MakersAsylumIndia/MAP6_Maker_Bee/datasheets/PngItem_3031532.png

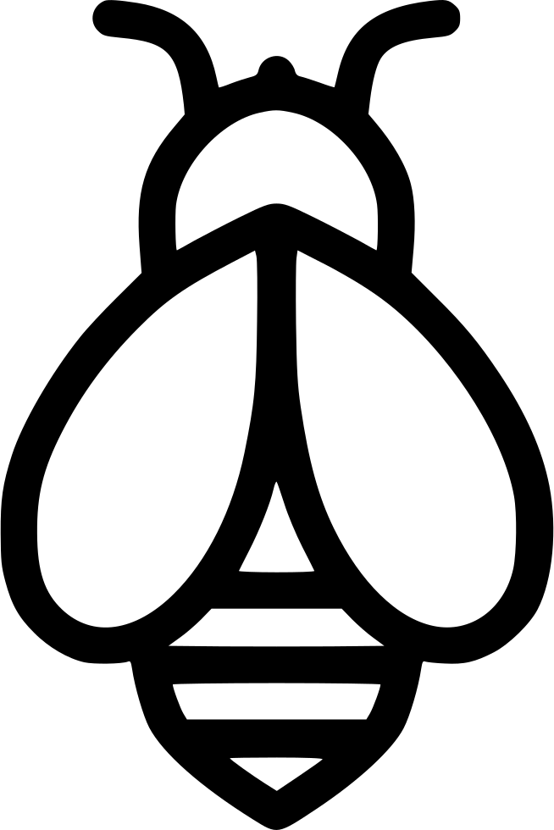
datasheets/PngItem_3031532.png
