MakersAsylumIndia/MAP6_Maker_Bee/kicad/images/MAP6-brd.png

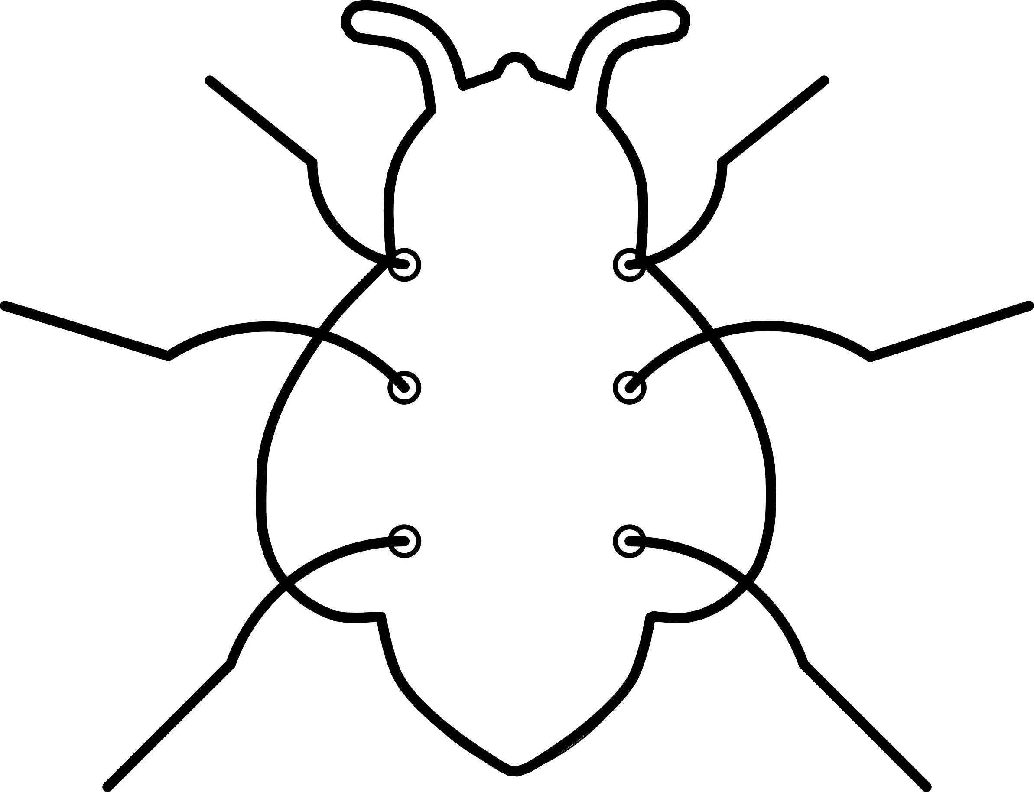
kicad/images/MAP6-brd.png
