MakersAsylumIndia/MAP6_Maker_Bee/kicad/images/MAP6_01.png

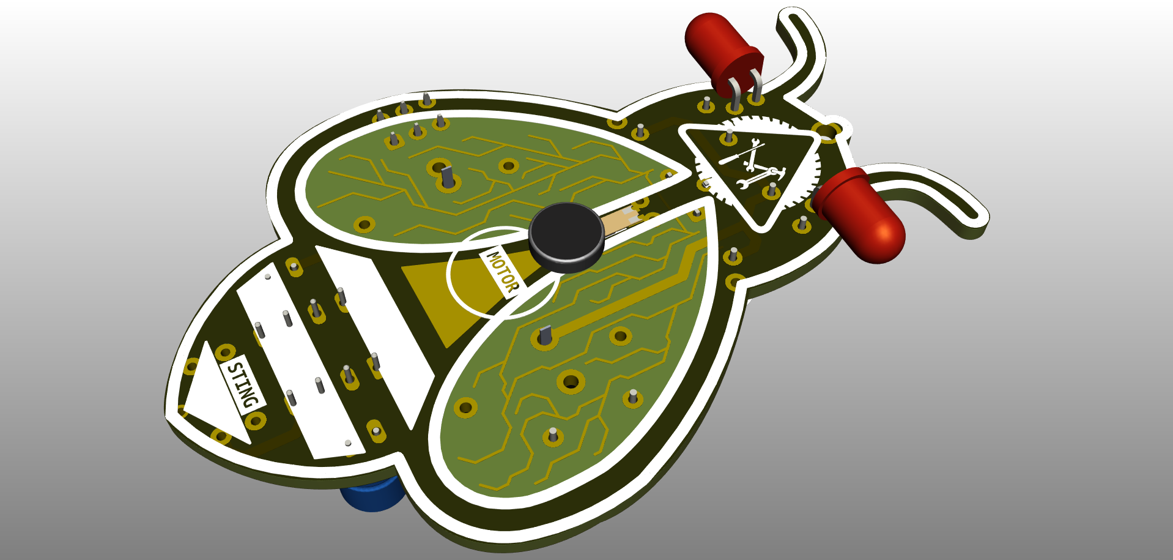
kicad/images/MAP6_01.png
