MakersAsylumIndia/MAP6_Maker_Bee/kicad/images/MAP6_02.png

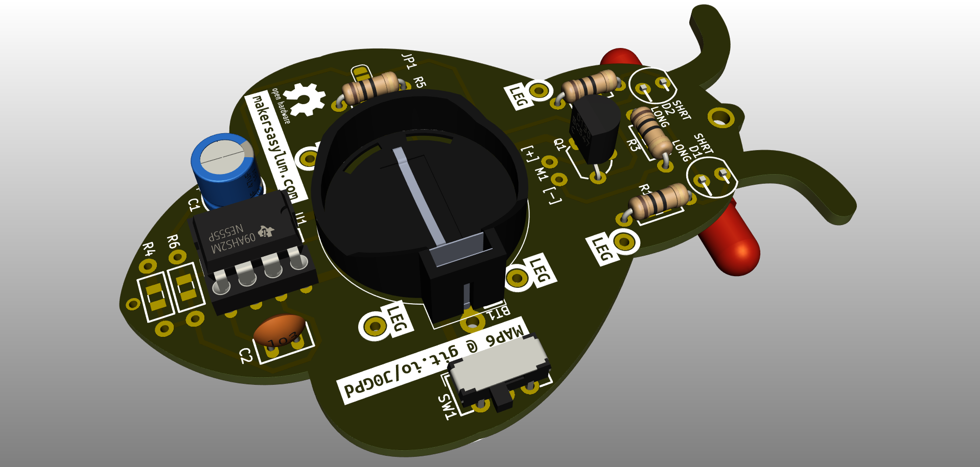
kicad/images/MAP6_02.png
