MakersAsylumIndia/MAP6_Maker_Bee/kicad/images/MAP6_03.png

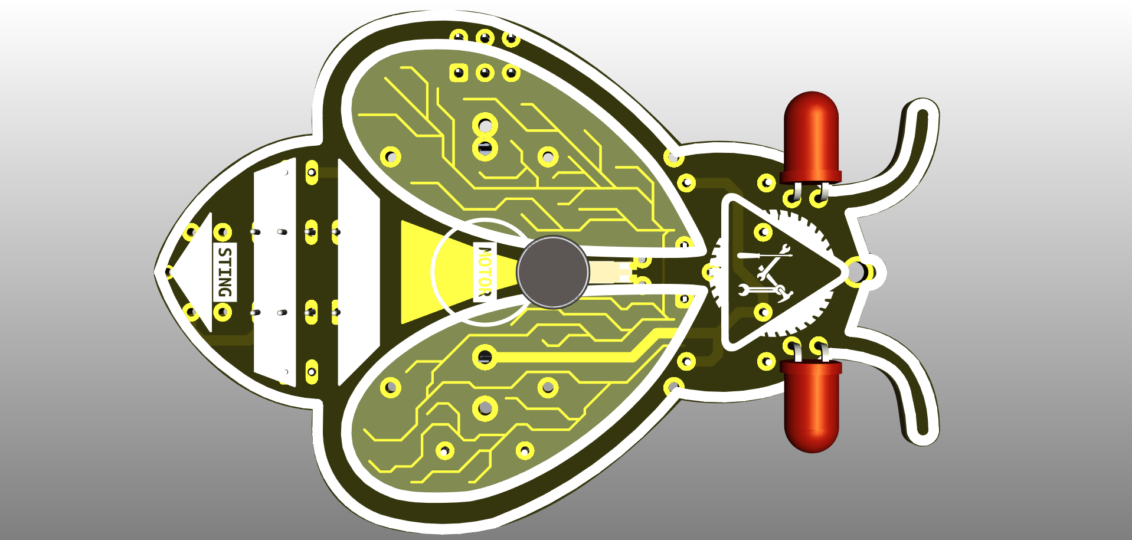
kicad/images/MAP6_03.png
