MakersAsylumIndia/MAP6_Maker_Bee/kicad/images/MAP6_04.png

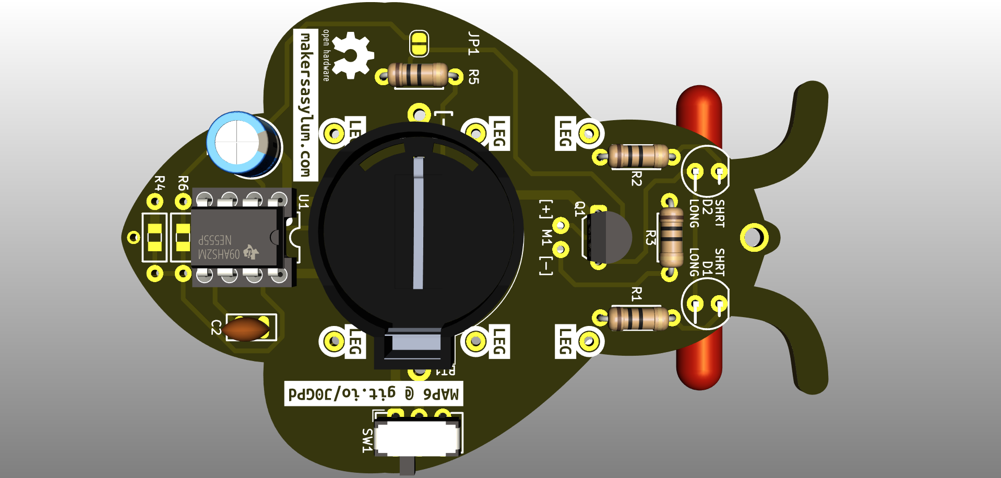
kicad/images/MAP6_04.png
