MakersAsylumIndia/MAP6_Maker_Bee/kicad/images/MAP6_05.png

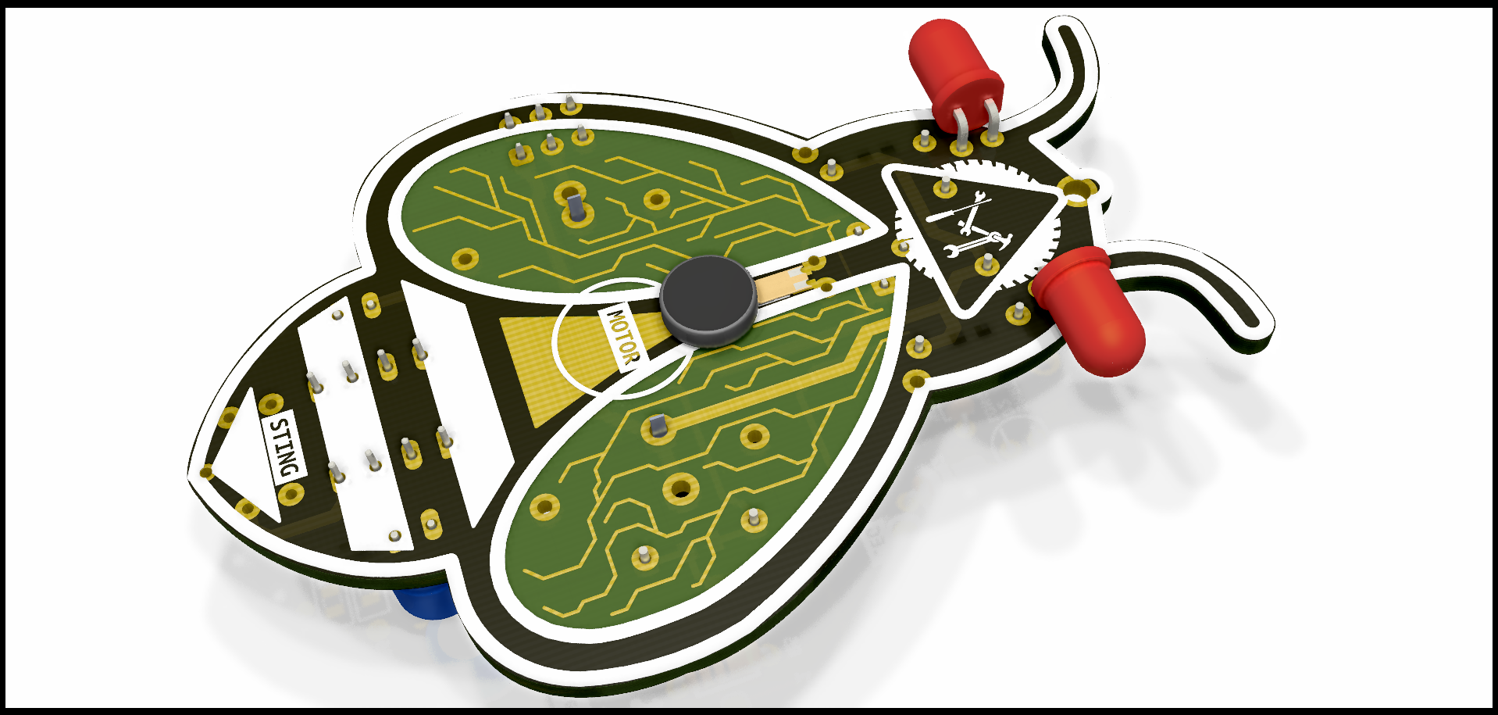
kicad/images/MAP6_05.png
