MakersAsylumIndia/MAP6_Maker_Bee/kicad/images/MAP6_06.png

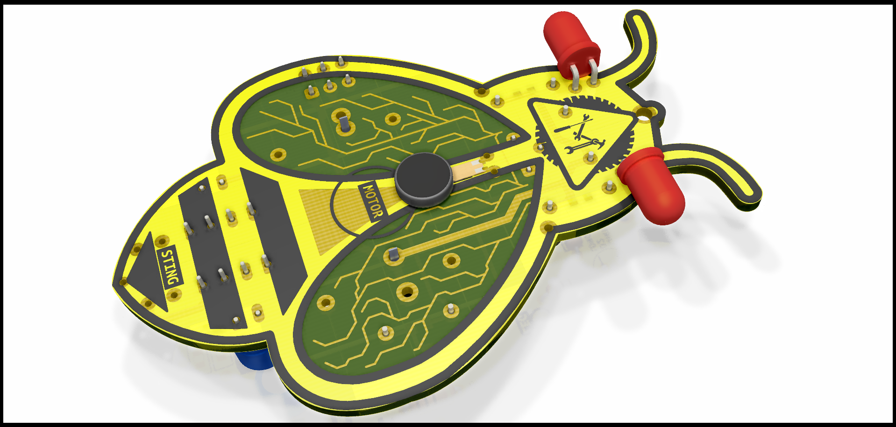
kicad/images/MAP6_06.png
