MakersAsylumIndia/MAP6_Maker_Bee/kicad/images/MAP6_07.png

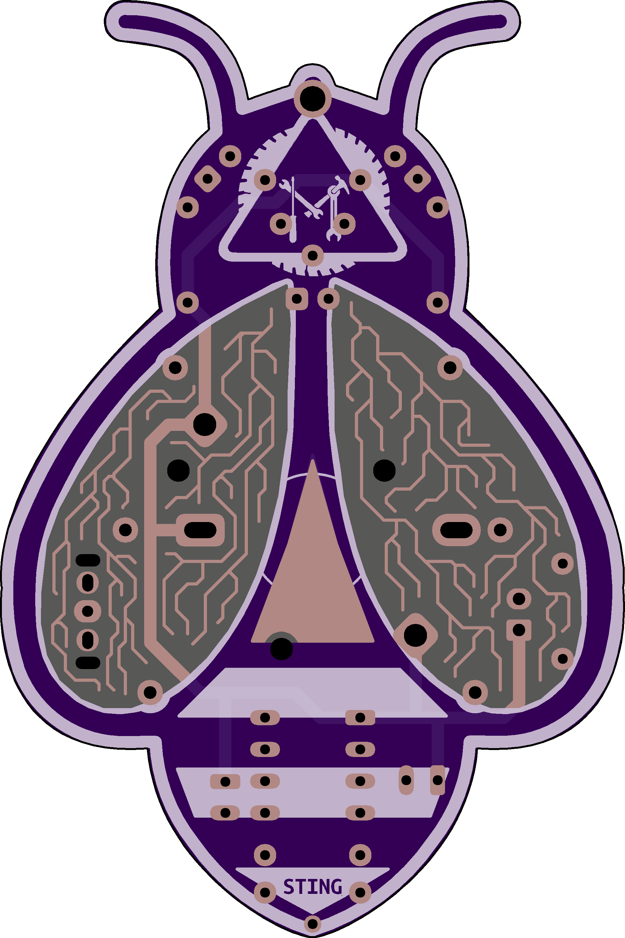
kicad/images/MAP6_07.png
