MakersAsylumIndia/MAP6_Maker_Bee/kicad/images/MAP6_08.png

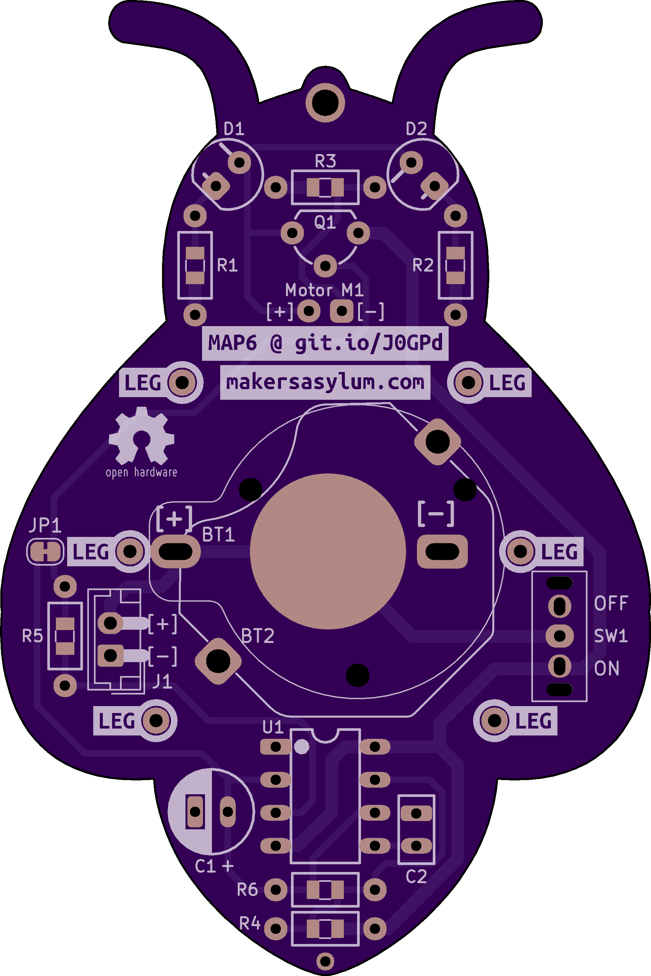
kicad/images/MAP6_08.png
