MakersAsylumIndia/MAP6_Maker_Bee/kicad/images/MAP6_13.png

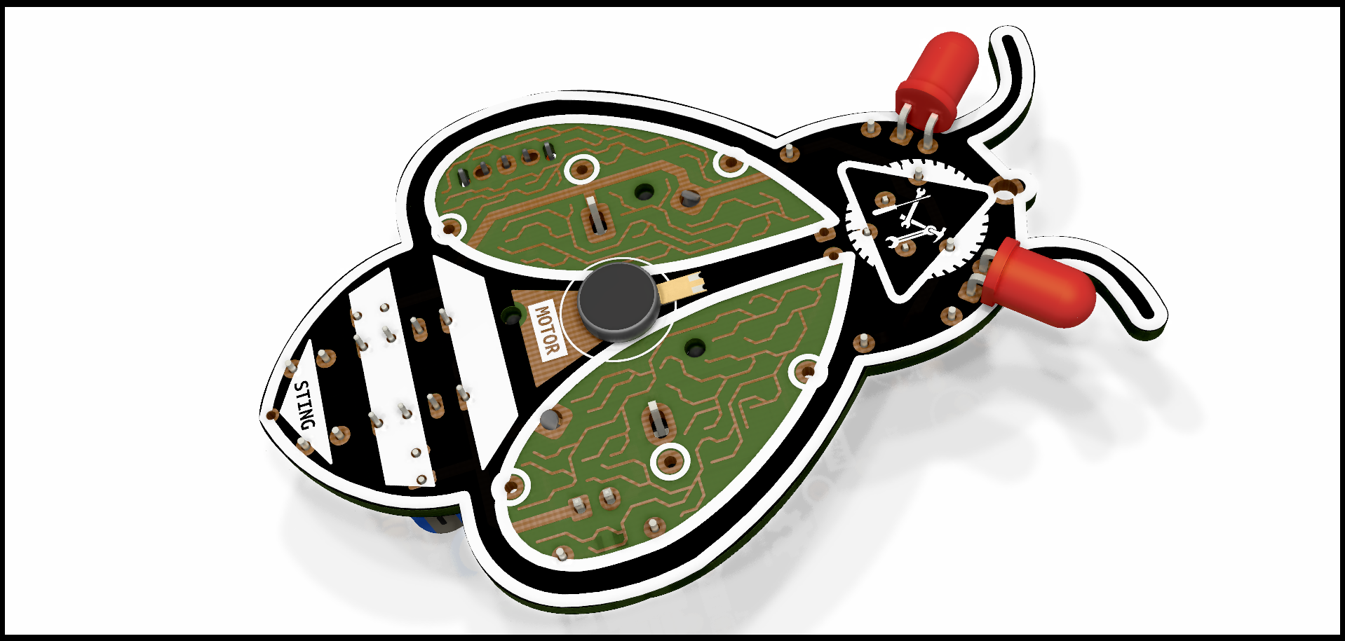
kicad/images/MAP6_13.png
