MakersAsylumIndia/MAP6_Maker_Bee/OSHWA_IN000031.png

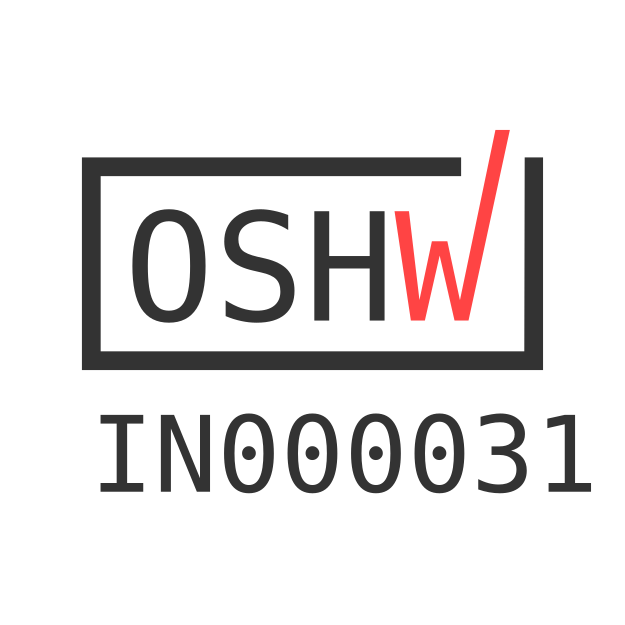
OSHWA_IN000031.png
