MakersAsylumIndia/MAP6_Maker_Bee/renders/map6_06_06_render12.png

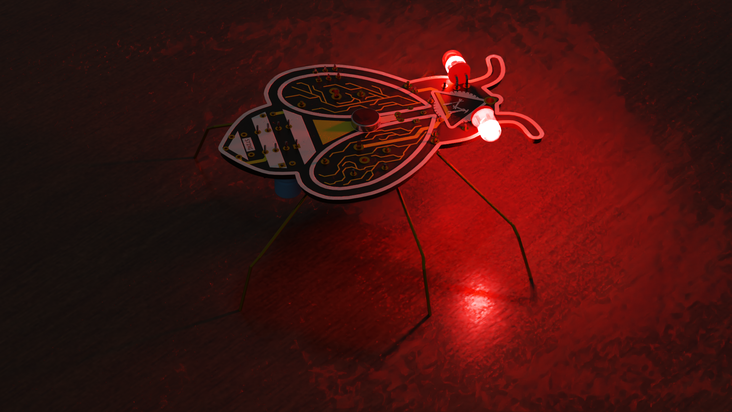
renders/map6_06_06_render12.png
