MakersAsylumIndia/MAP6_Maker_Bee/renders/map6_render02.png

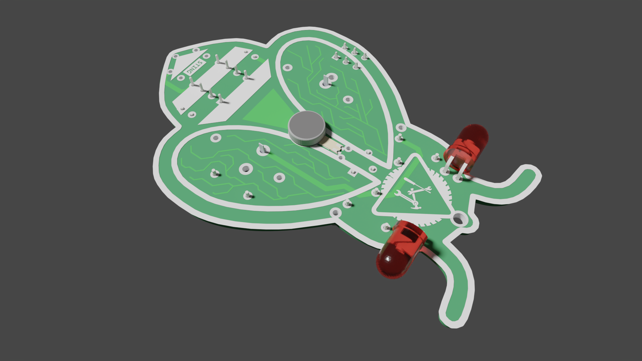
renders/map6_render02.png
