MakersAsylumIndia/MAP6_Maker_Bee/renders/map6_render03.jpg

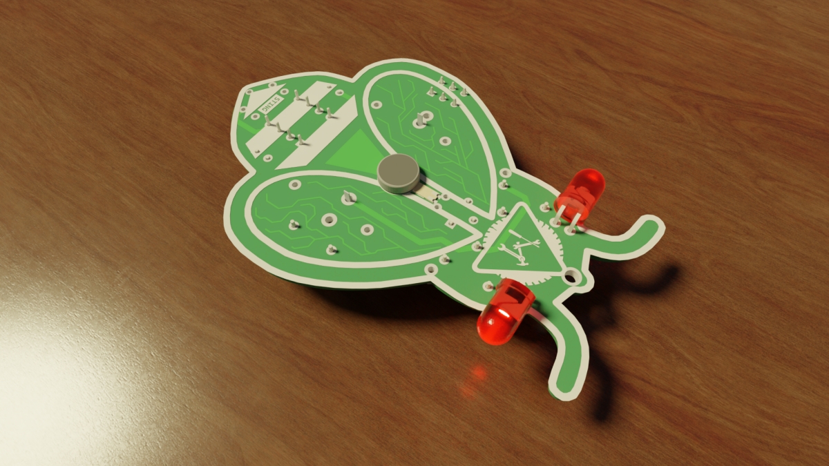
renders/map6_render03.jpg
