MakersAsylumIndia/MAP6_Maker_Bee/renders/map6_render05.jpg

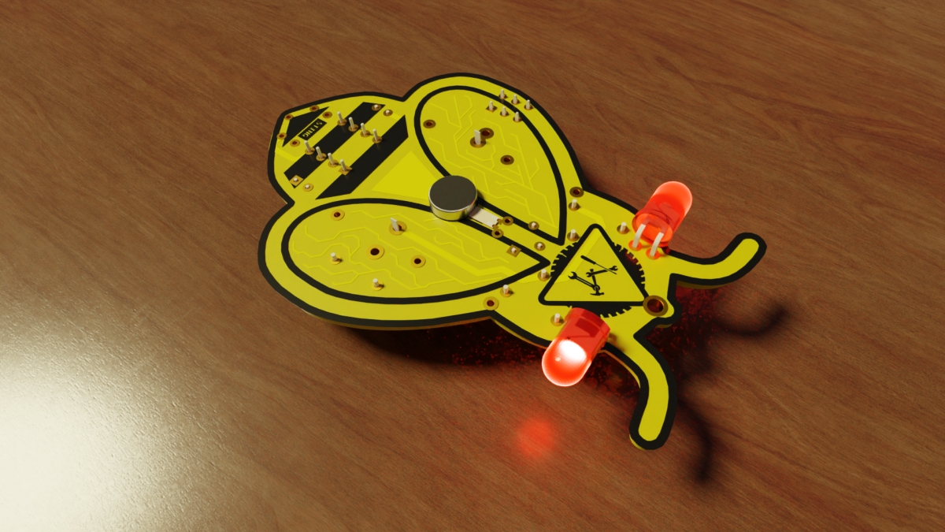
renders/map6_render05.jpg
