MakersAsylumIndia/MAP6_Maker_Bee/renders/map6_render07.jpg

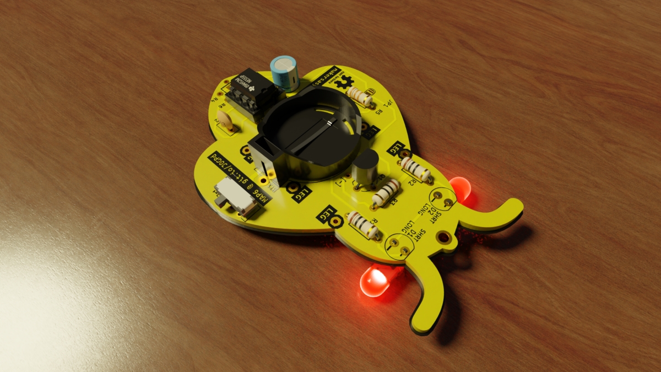
renders/map6_render07.jpg
