MakersAsylumIndia/MAP6_Maker_Bee/renders/map6_render09.jpg

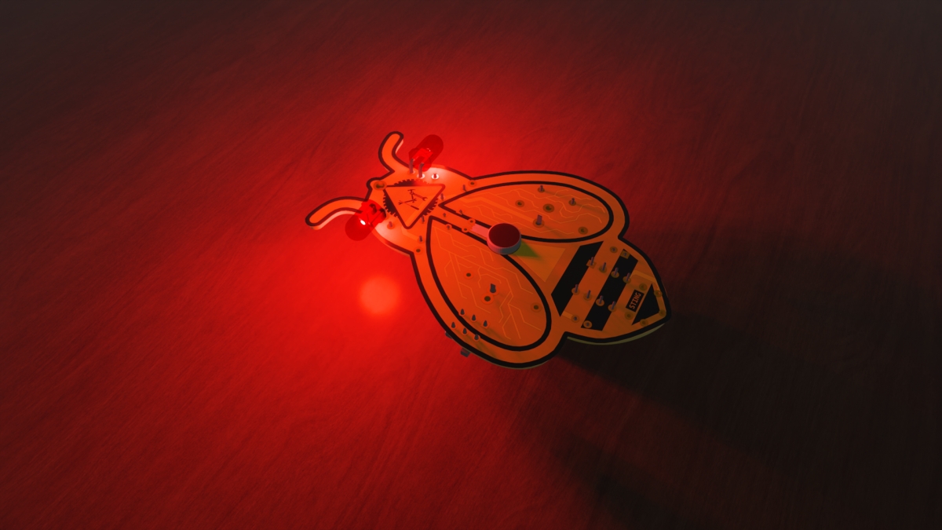
renders/map6_render09.jpg
