MakersAsylumIndia/MAP6_Maker_Bee/renders/map6_render10.jpg

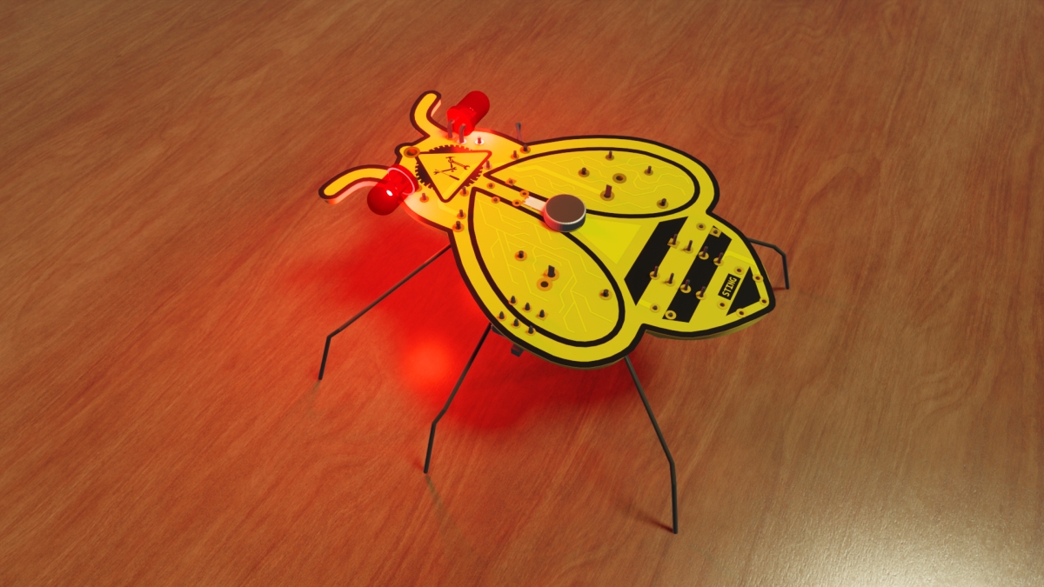
renders/map6_render10.jpg
