MakersAsylumIndia/MAP6_Maker_Bee/renders/map6_render11.png

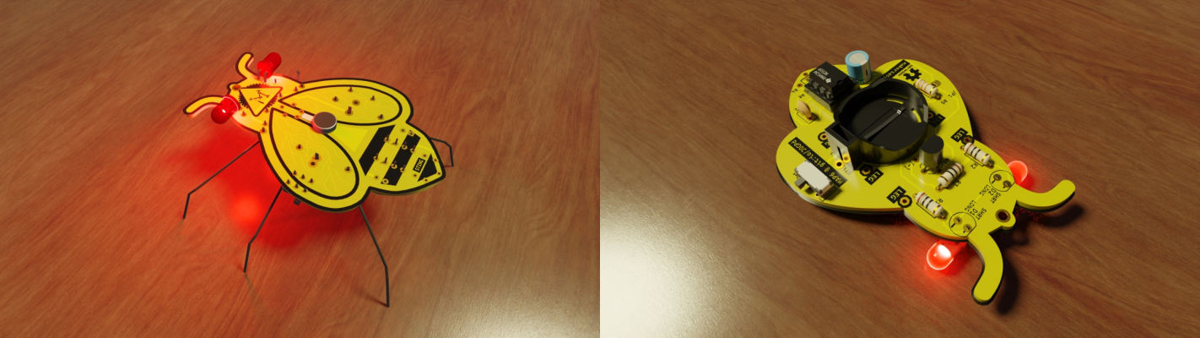
renders/map6_render11.png
