MakersAsylumIndia/MAP6_Maker_Bee/fabricate/PCB_outline/shape_bee5.dxf

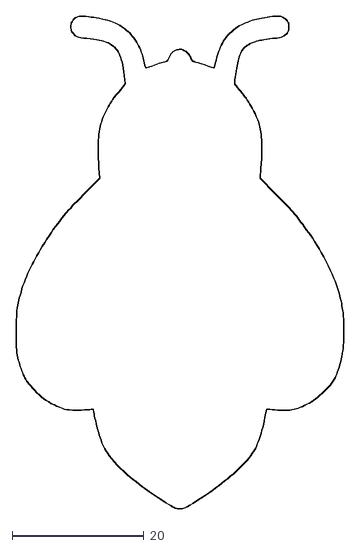
[picture p39: CAD file, 2021-08-18]
fabricate/PCB_outline/shape_bee5.dxf
49.8 x 74.9
