MakersAsylumIndia/MAP6_Maker_Bee/nightly/3d_modules/JST_EH_B3B-EH-A_1x03_P2.50mm_Vertical.step

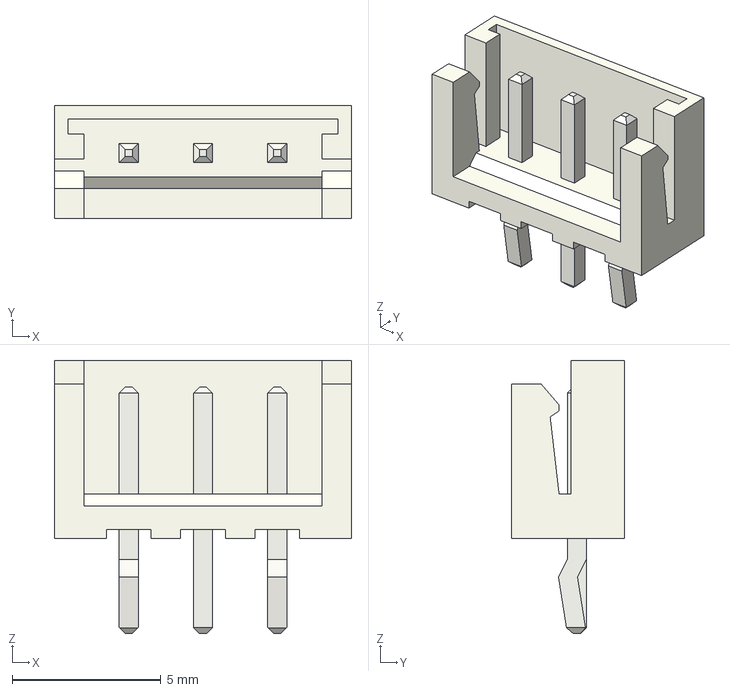
[picture p40: CAD file, 2021-09-08]
nightly/3d_modules/JST_EH_B3B-EH-A_1x03_P2.50mm_Vertical.step
10.0 x 3.80 x 9.20 mm
