MakersAsylumIndia/MAP6_Maker_Bee/fabricate/PCB_outline/outline_bee.dxf

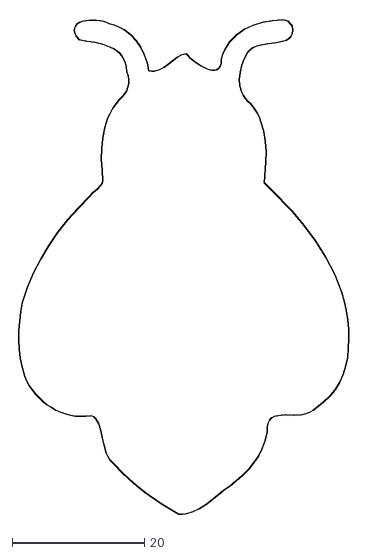
[picture p41: CAD file, 2021-08-18]
fabricate/PCB_outline/outline_bee.dxf
51.0 x 75.5
