MakersAsylumIndia/MAP6_Maker_Bee/kicad/3d_modules/JST_EH_B2B-EH-A_1x02_P2.50mm_Vertical.step

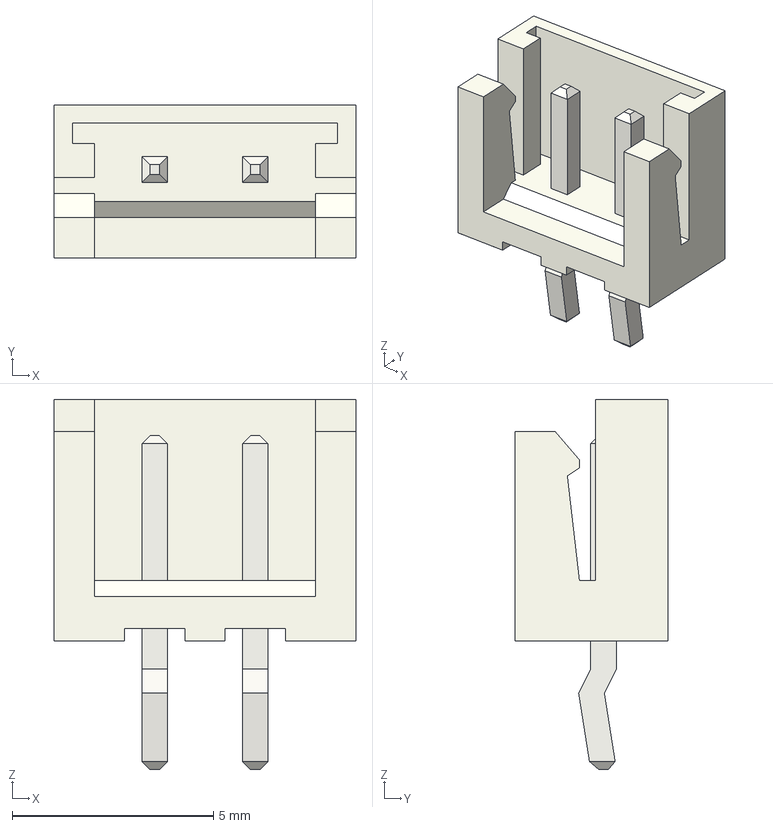
[picture p42: CAD file, 2021-09-08]
kicad/3d_modules/JST_EH_B2B-EH-A_1x02_P2.50mm_Vertical.step
7.50 x 3.80 x 9.20 mm
