MakersAsylumIndia/MAP6_Maker_Bee/nightly/3d_modules/CR2032_cyl_cp.step

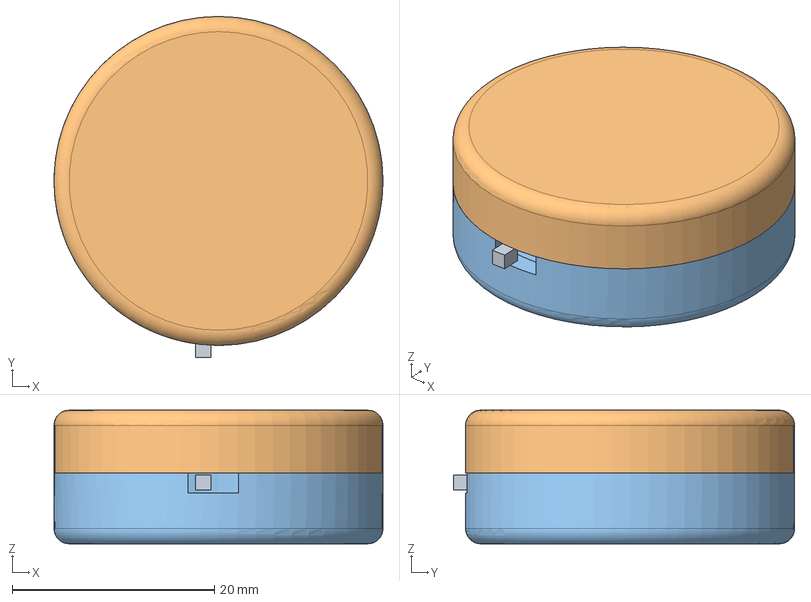
[picture p44: CAD file, 2021-09-07]
nightly/3d_modules/CR2032_cyl_cp.step
32.5 x 33.7 x 13.2 mm
