MakersAsylumIndia/MAP6_Maker_Bee/fabricate/PCB_outline/shape_bee3.dxf

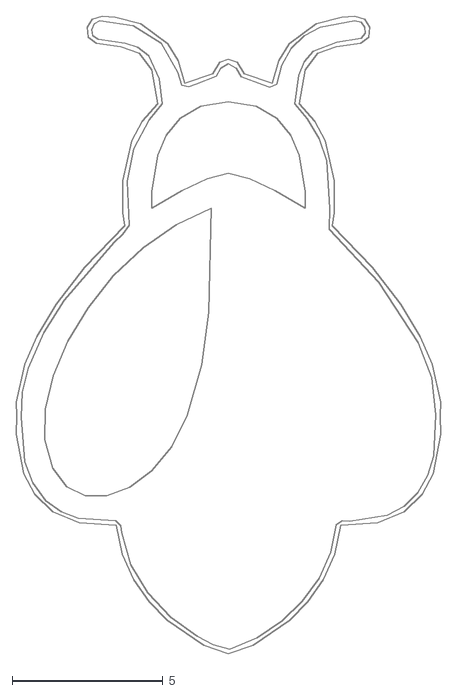
[picture p45: CAD file, 2021-08-18]
fabricate/PCB_outline/shape_bee3.dxf
14.1 x 21.1
