MakersAsylumIndia/MAP6_Maker_Bee/fabricate/PCB_outline/outline_bee2.dxf

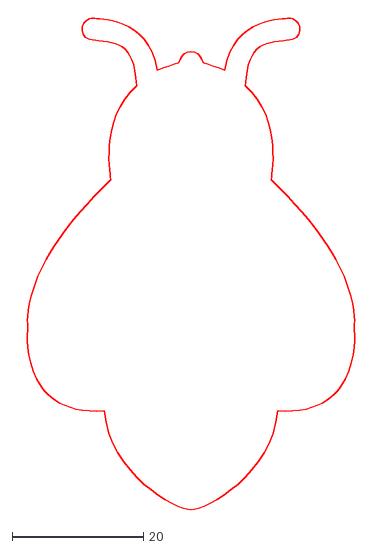
[picture p46: CAD file, 2021-08-18]
fabricate/PCB_outline/outline_bee2.dxf
53.2 x 75.2
