MakersAsylumIndia/MAP6_Maker_Bee/fabricate/PCB_outline/shape_bee4.dxf

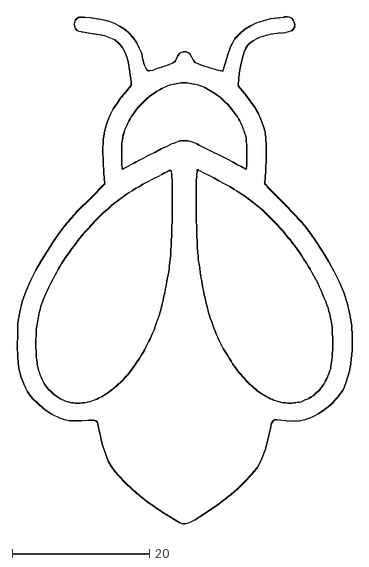
[picture p47: CAD file, 2021-08-18]
fabricate/PCB_outline/shape_bee4.dxf
49.0 x 74.3
