MakersAsylumIndia/MAP6_Maker_Bee/nightly/3d_modules/Led5mm_right_FC.step

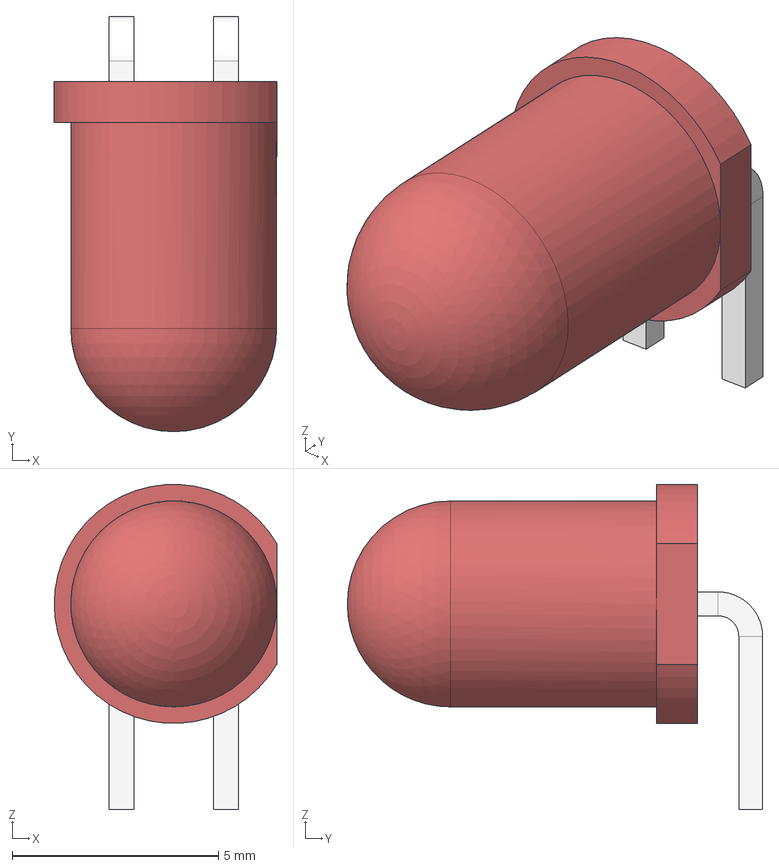
[picture p48: CAD file, 2021-08-23]
nightly/3d_modules/Led5mm_right_FC.step
5.40 x 10.1 x 7.89 mm
