MakersAsylumIndia/MAP6_Maker_Bee/nightly/3d_modules/TO-92_BC547_FC.step

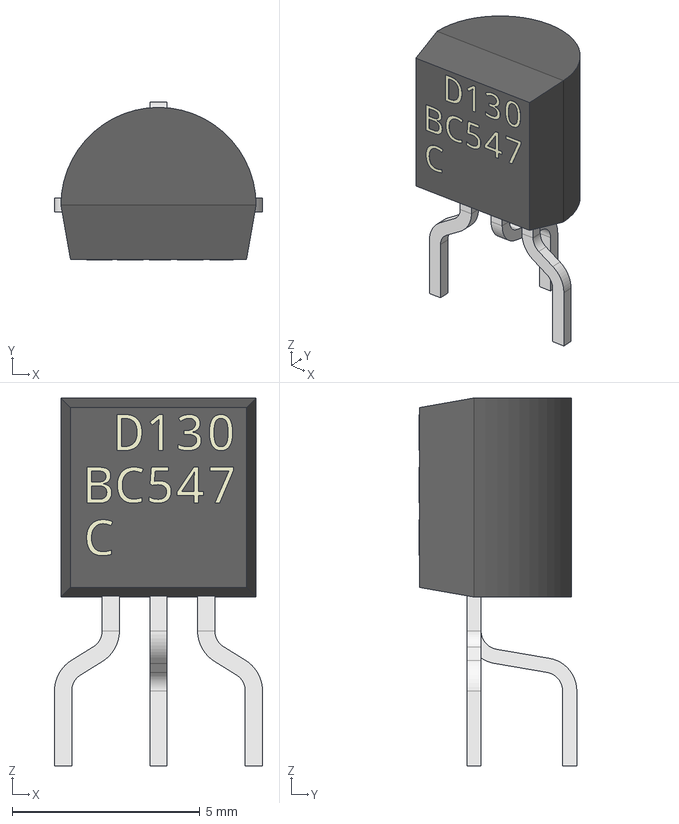
[picture p49: CAD file, 2021-08-23]
nightly/3d_modules/TO-92_BC547_FC.step
5.54 x 4.20 x 9.80 mm
