MakersAsylumIndia/MAP6_Maker_Bee/nightly/3d_modules/C_Disc_D50mm_W25mm_P250mm.step

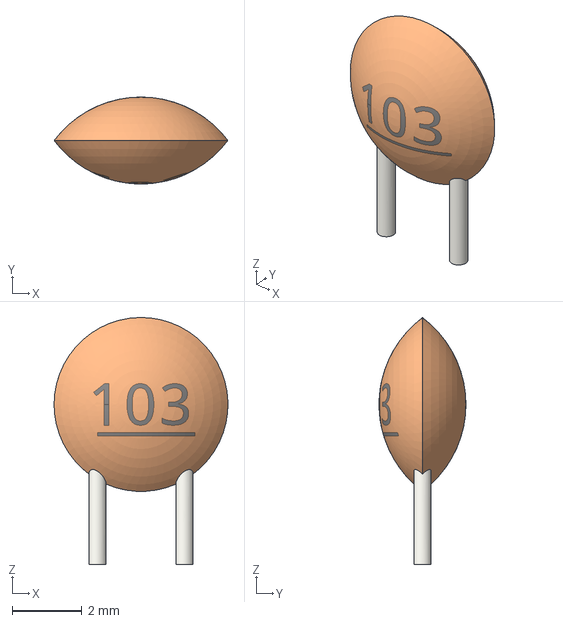
[picture p50: CAD file, 2021-08-23]
nightly/3d_modules/C_Disc_D50mm_W25mm_P250mm.step
5.00 x 2.50 x 7.10 mm
