MakersAsylumIndia/MAP6_Maker_Bee/nightly/3d_modules/CP_Radial_D63mm_P25mm.FCStd

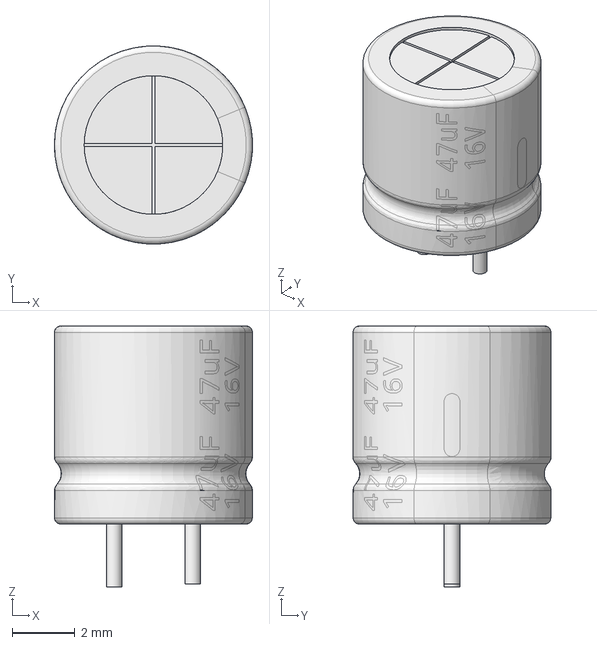
[picture p51: CAD file, 2021-08-23]
nightly/3d_modules/CP_Radial_D63mm_P25mm.FCStd
6.30 x 6.30 x 8.30 mm
