MakersAsylumIndia/MAP6_Maker_Bee/nightly/3d_modules/R_Axial_DIN0207_L6_3mm_D2_5mm_P7_62mm_Horizontal_33k.step

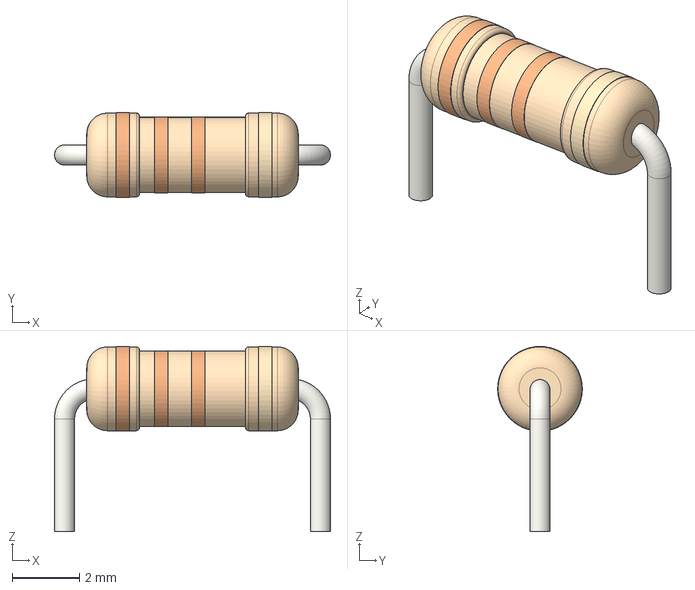
[picture p52: CAD file, 2021-08-23]
nightly/3d_modules/R_Axial_DIN0207_L6_3mm_D2_5mm_P7_62mm_Horizontal_33k.step
8.22 x 2.52 x 5.51 mm
