MakersAsylumIndia/MAP6_Maker_Bee/nightly/3d_modules/DIP-8_W762mm.step

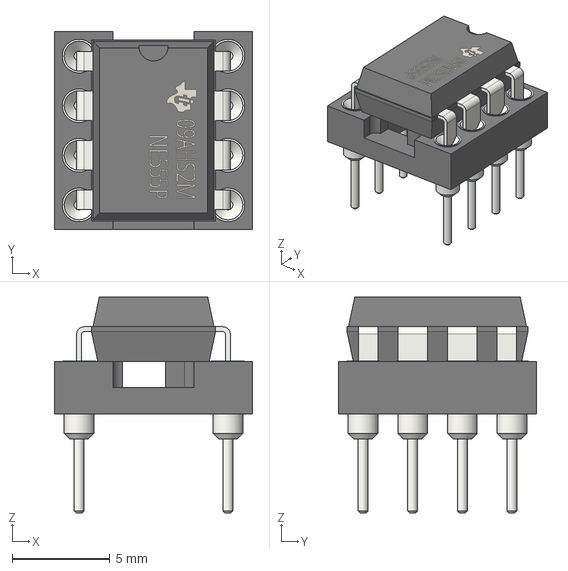
[picture p53: CAD file, 2021-08-23]
nightly/3d_modules/DIP-8_W762mm.step
10.2 x 10.2 x 11.1 mm
