MakersAsylumIndia/MAP6_Maker_Bee/nightly/3d_modules/DIP-8_W762mm_FC.step

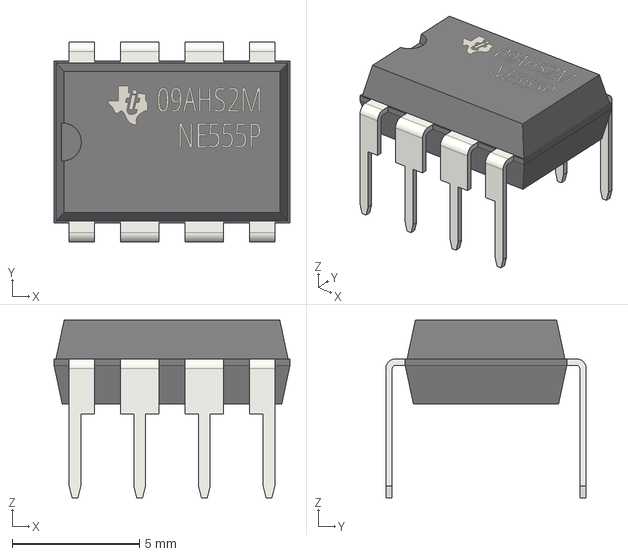
[picture p54: CAD file, 2021-08-23]
nightly/3d_modules/DIP-8_W762mm_FC.step
9.27 x 7.87 x 6.98 mm
