MakersAsylumIndia/MAP6_Maker_Bee/nightly/3d_modules/SW_CuK_JS202011AQN_DPDT_Angled.step

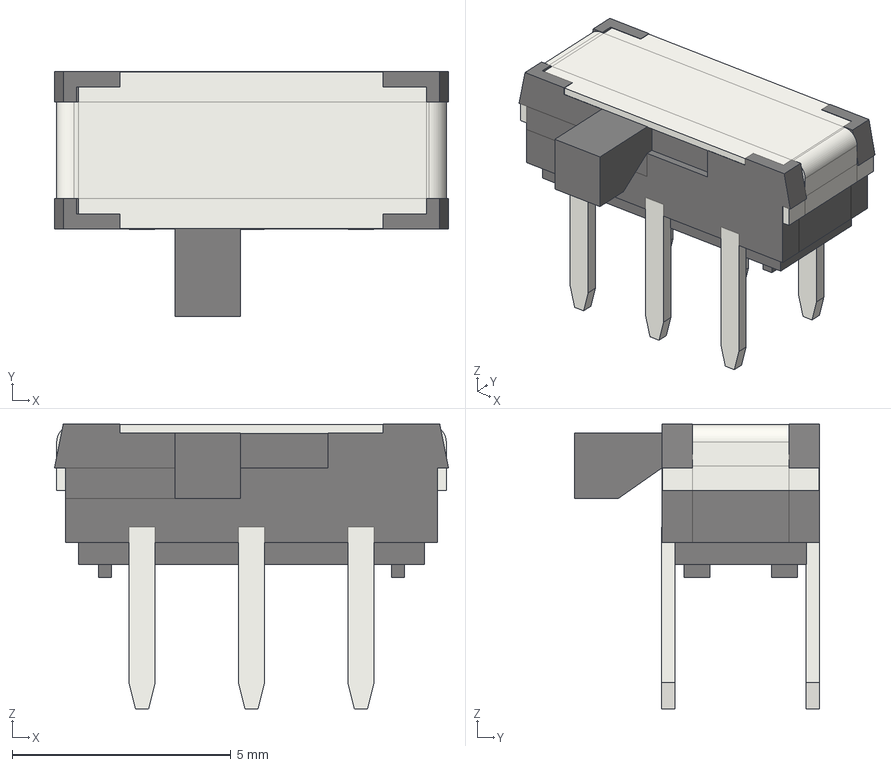
[picture p55: CAD file, 2021-08-18]
nightly/3d_modules/SW_CuK_JS202011AQN_DPDT_Angled.step
9.00 x 5.61 x 6.50 mm
