MakersAsylumIndia/MAP6_Maker_Bee/nightly/3d_modules/CR2032_HOR_HOLD.step

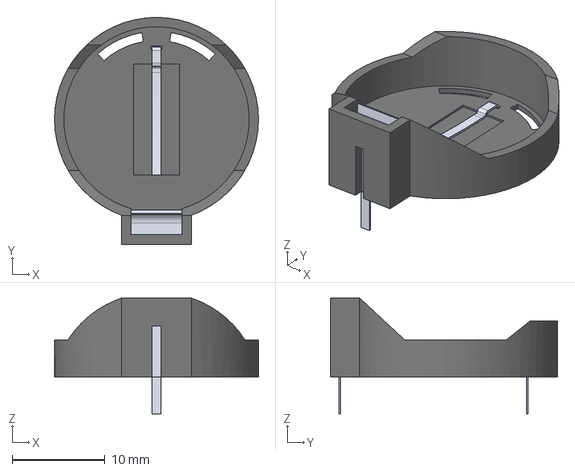
[picture p56: CAD file, 2021-08-18]
nightly/3d_modules/CR2032_HOR_HOLD.step
22.0 x 24.5 x 12.5 mm
