MakersAsylumIndia/MAP6_Maker_Bee/nightly/3d_modules/BATTERY_HOLDER_CR2032.step

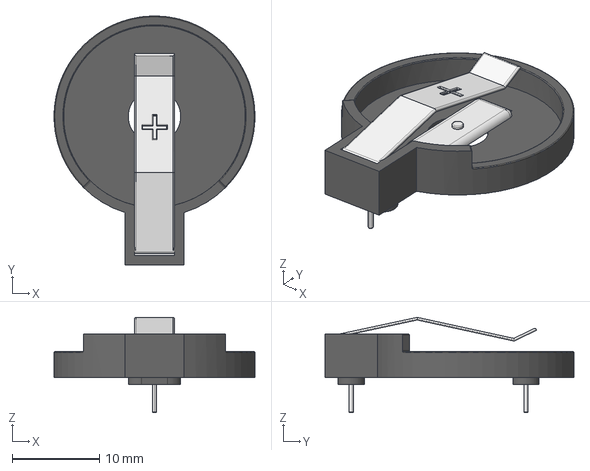
[picture p57: CAD file, 2021-08-18]
nightly/3d_modules/BATTERY_HOLDER_CR2032.step
23.0 x 28.5 x 10.9 mm
