MakersAsylumIndia/MAP6_Maker_Bee/nightly/3d_modules/DIP-8_W7.62mm_Socket.step

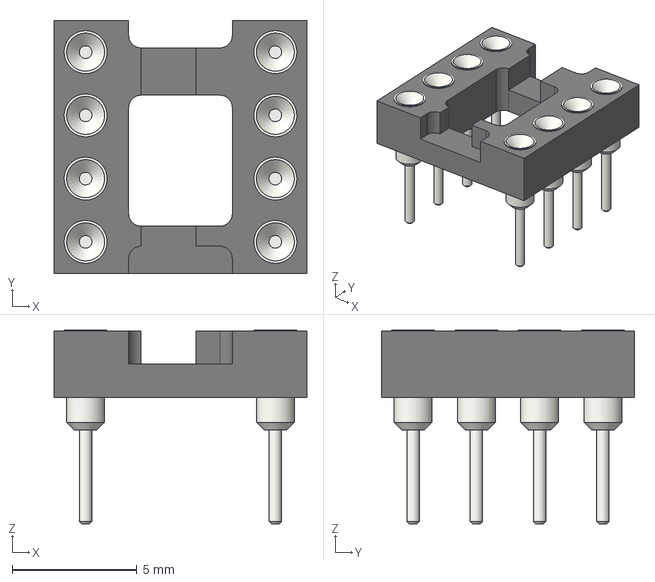
[picture p58: CAD file, 2021-08-18]
nightly/3d_modules/DIP-8_W7.62mm_Socket.step
10.2 x 10.2 x 7.79 mm
