MakersAsylumIndia/MAP6_Maker_Bee/fabricate/images/MAP6_assy_08.png

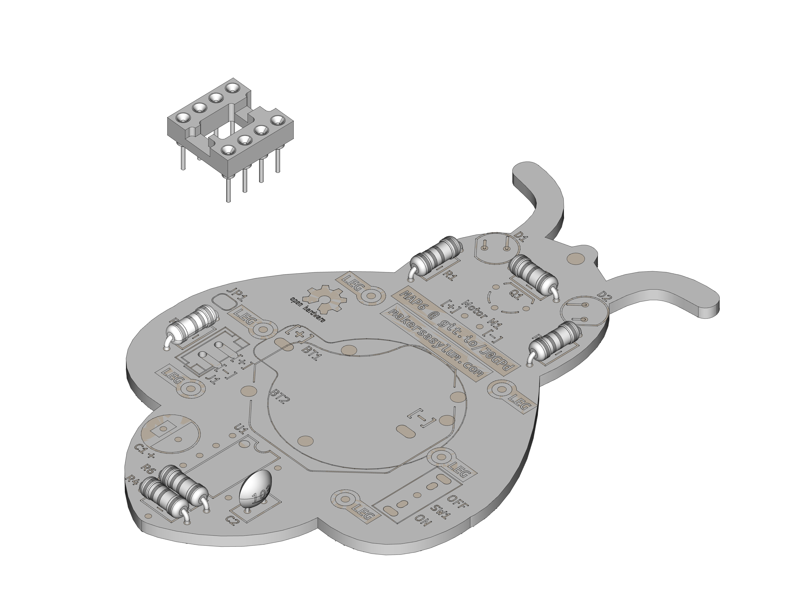
fabricate/images/MAP6_assy_08.png
