MakersAsylumIndia/MAP6_Maker_Bee/fabricate/images/MAP6_assy_09.png

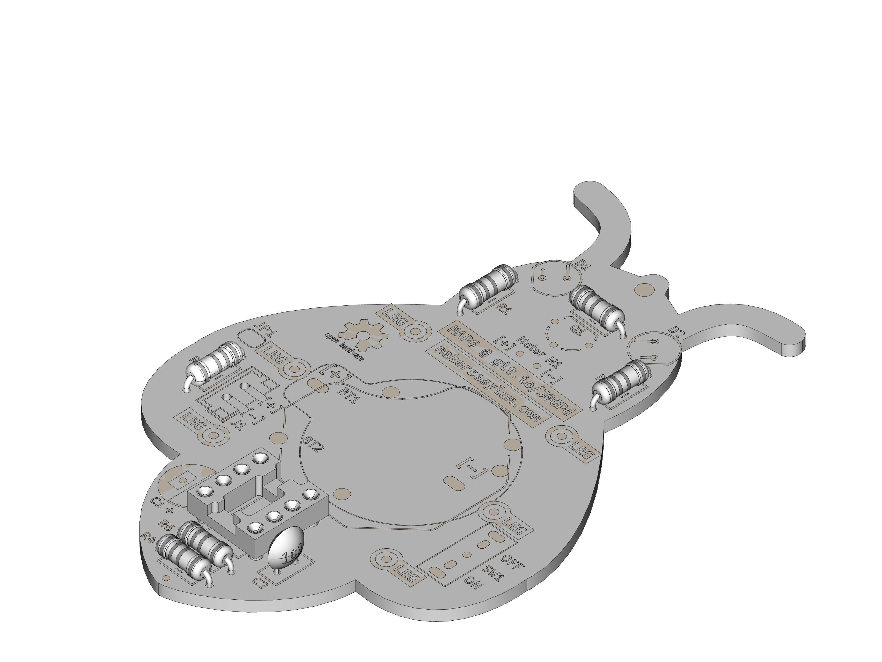
fabricate/images/MAP6_assy_09.png
