MakersAsylumIndia/MAP6_Maker_Bee/fabricate/images/MAP6_assy_21.png

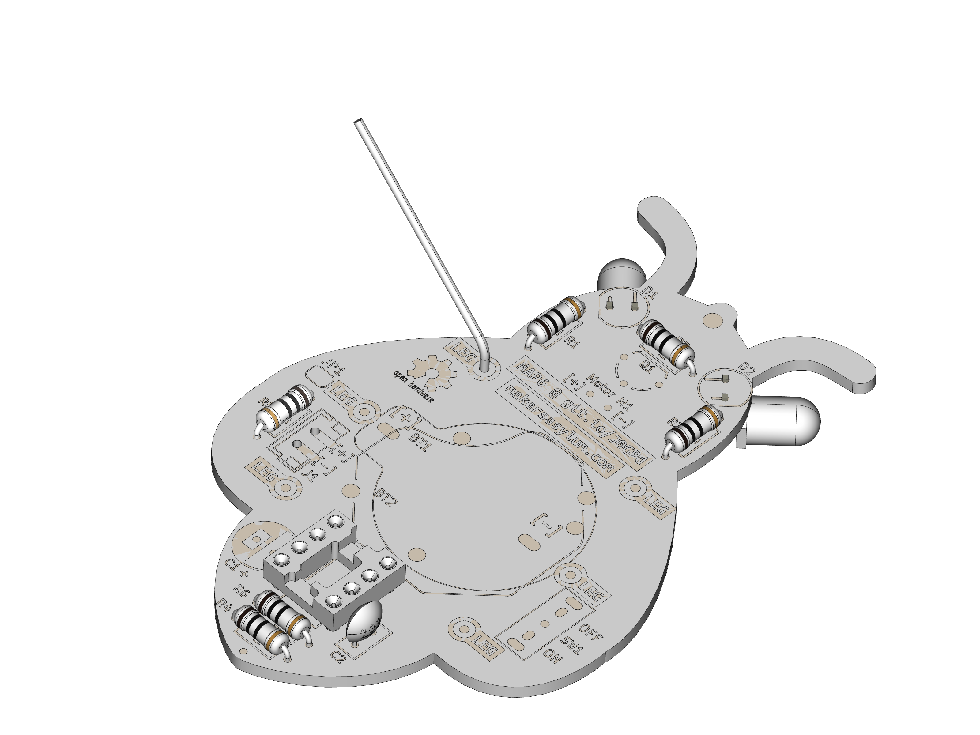
fabricate/images/MAP6_assy_21.png
