MakersAsylumIndia/MAP6_Maker_Bee/fabricate/images/MG_2371-edit.jpg

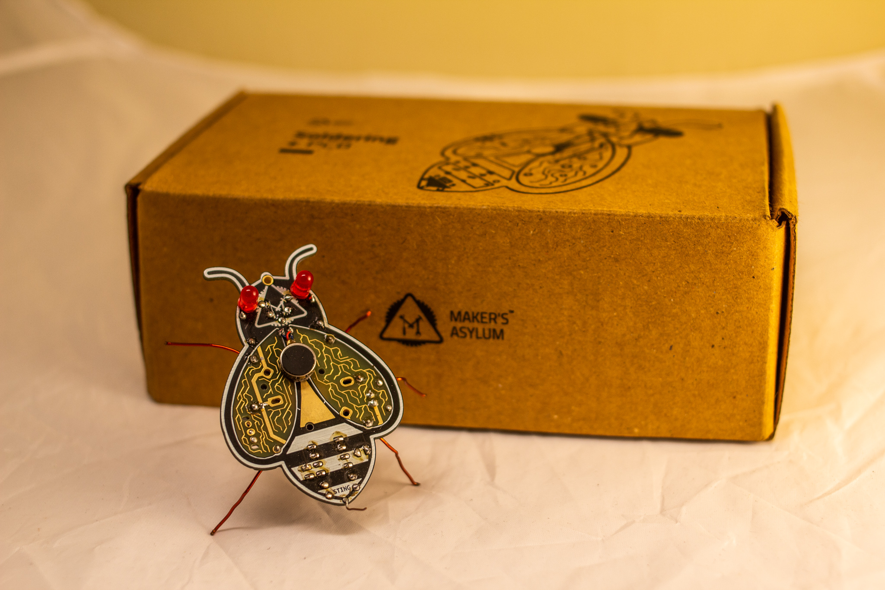
fabricate/images/MG_2371-edit.jpg
