MakersAsylumIndia/MAP6_Maker_Bee/fabricate/images/MG_2401-scaled.jpg

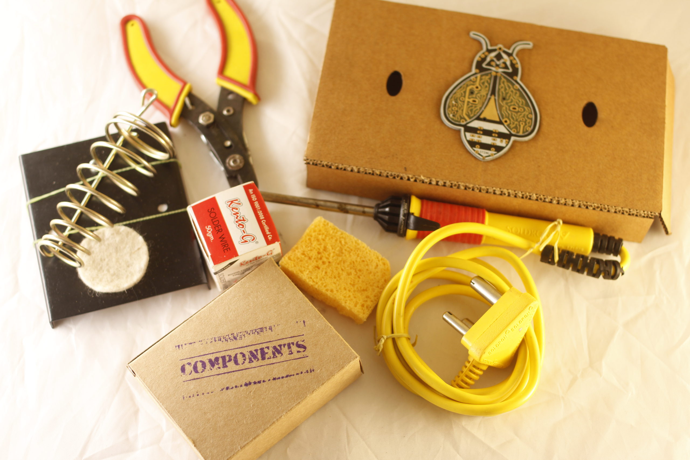
fabricate/images/MG_2401-scaled.jpg
